meerstern/UsbFilterBoard/pcb/uf.sch

## KiCad design pcb/uf.sch (2024-04-13)

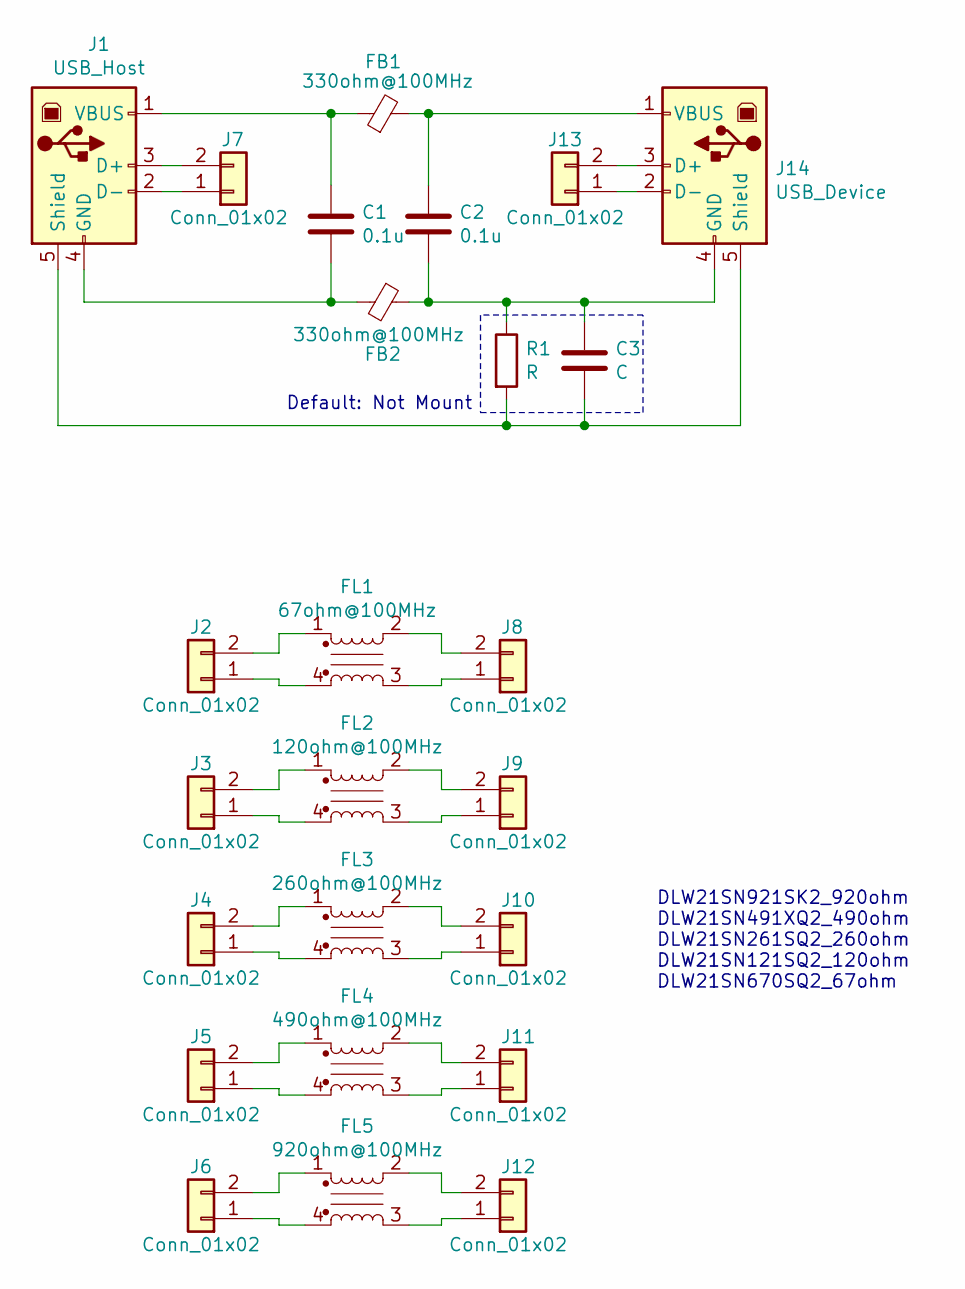
[picture p7: schematic uf.sch]

Parts:
C1, C2: 0.1u; C_0603_1608Metric
C3: C; C_0603_1608Metric
FB1, FB2: 330ohm@100MHz; L_0805_2012Metric
FL1: 67ohm@100MHz; L_CommonModeChoke_Coilcraft_0805USB
FL2: 120ohm@100MHz; L_CommonModeChoke_Coilcraft_0805USB
FL3: 260ohm@100MHz; L_CommonModeChoke_Coilcraft_0805USB
FL4: 490ohm@100MHz; L_CommonModeChoke_Coilcraft_0805USB
FL5: 920ohm@100MHz; L_CommonModeChoke_Coilcraft_0805USB
J1: USB_Host; USBHOST
J2, J3, J4, J5, J6, J7, J8, J9, J10, J11, J12, J13: Conn_01x02; PinHeader_1x02_P2.54mm_Vertical
J14: USB_Device; USBA
R1: R; R_0603_1608Metric

Connections:
unnamed: C1.1, FB1.1, J1.1 (VBUS)
unnamed: C1.2, FB2.2, J1.4 (GND)
unnamed: C2.1, FB1.2, J14.1 (VBUS)
unnamed: C2.2, C3.1, FB2.1, J14.4 (GND), R1.1
unnamed: C3.2, J1.5 (Shield), J14.5 (Shield), R1.2
unnamed: FL1.1, J2.2
unnamed: FL1.2, J8.2
unnamed: FL1.3, J8.1
unnamed: FL1.4, J2.1
unnamed: FL2.1, J3.2
unnamed: FL2.2, J9.2
unnamed: FL2.3, J9.1
unnamed: FL2.4, J3.1
unnamed: FL3.1, J4.2
unnamed: FL3.2, J10.2
unnamed: FL3.3, J10.1
unnamed: FL3.4, J4.1
unnamed: FL4.1, J5.2
unnamed: FL4.2, J11.2
unnamed: FL4.3, J11.1
unnamed: FL4.4, J5.1
unnamed: FL5.1, J6.2
unnamed: FL5.2, J12.2
unnamed: FL5.3, J12.1
unnamed: FL5.4, J6.1
unnamed: J1.2 (D-), J7.1
unnamed: J1.3 (D+), J7.2
unnamed: J13.1, J14.2 (D-)
unnamed: J13.2, J14.3 (D+)

Notes on the sheet:
DLW21SN921SK2_920ohm DLW21SN491XQ2_490ohm DLW21SN261SQ2_260ohm DLW21SN121SQ2_120ohm DLW21SN670SQ2_67ohm
Default: Not Mount
